jpenalta/fragolinos-medidorCO2/imaxes/alumnos_montando.jpg

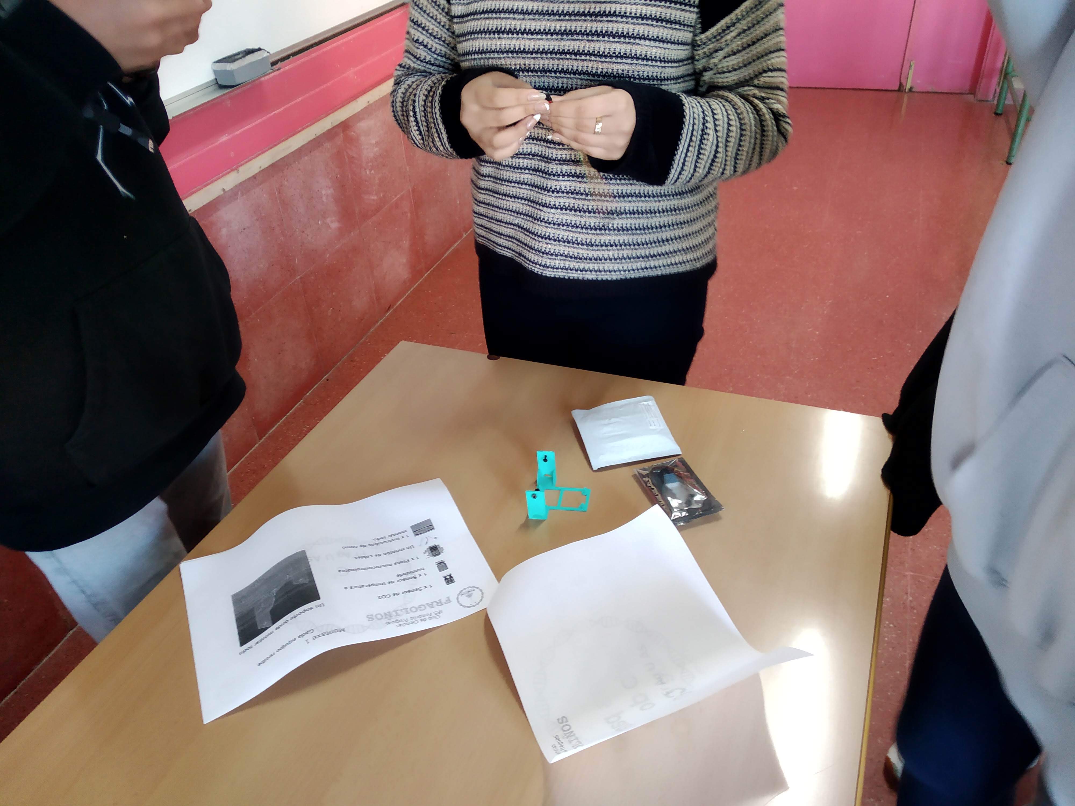
imaxes/alumnos_montando.jpg
