jpenalta/fragolinos-medidorCO2/imaxes/preparados_para_a_aula_2.jpg

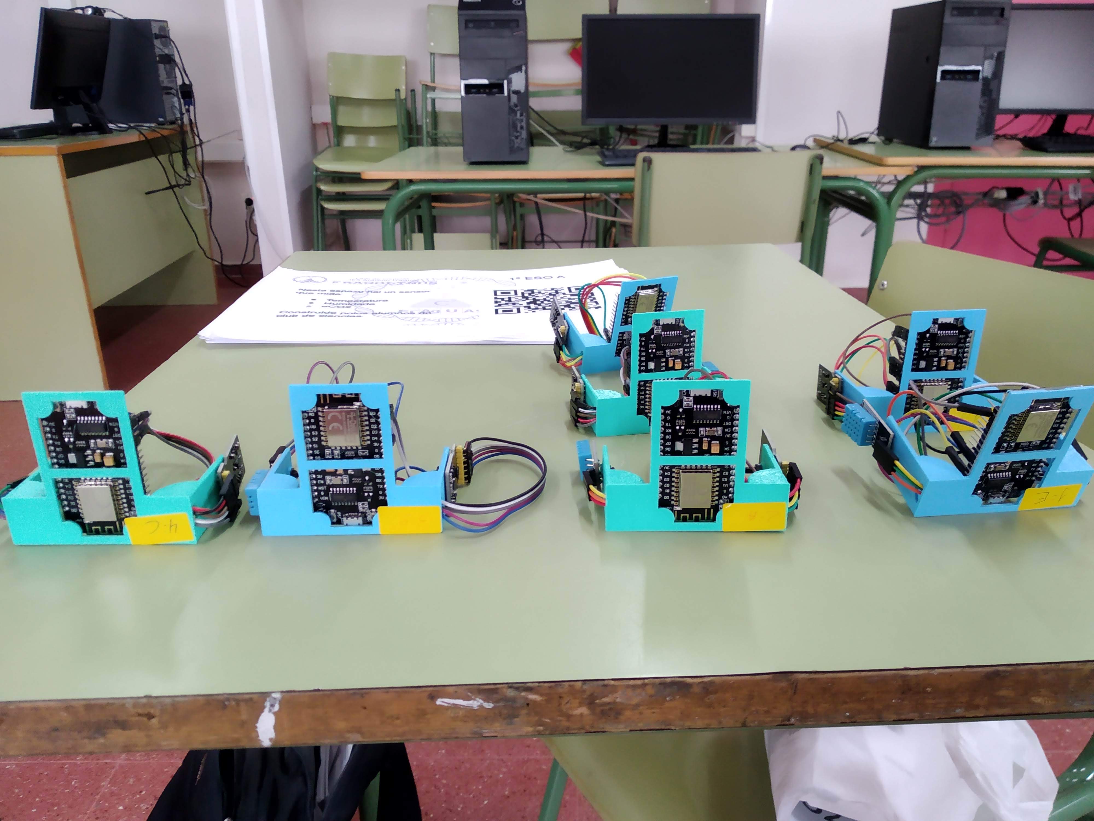
imaxes/preparados_para_a_aula_2.jpg
