jpenalta/fragolinos-medidorCO2/imaxes/soportes_1.jpg

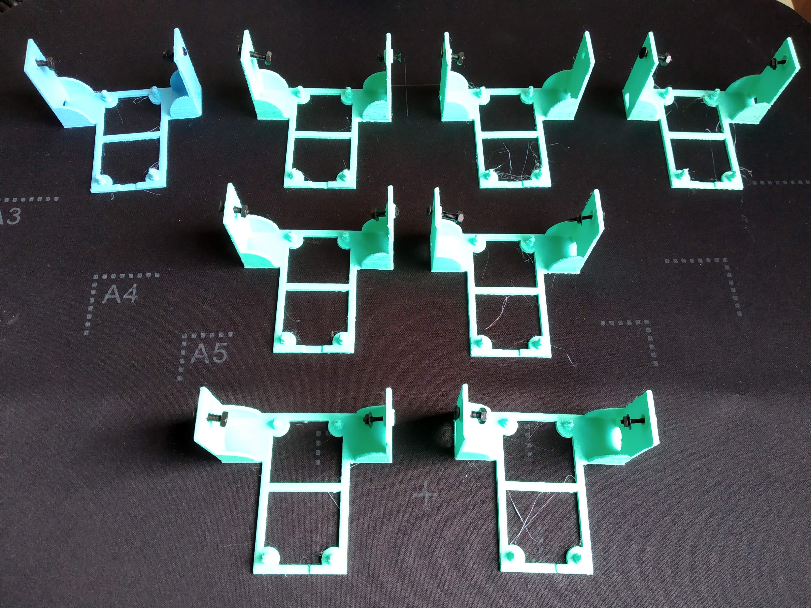
imaxes/soportes_1.jpg
