jpenalta/fragolinos-medidorCO2/imaxes/soportes_2.jpg

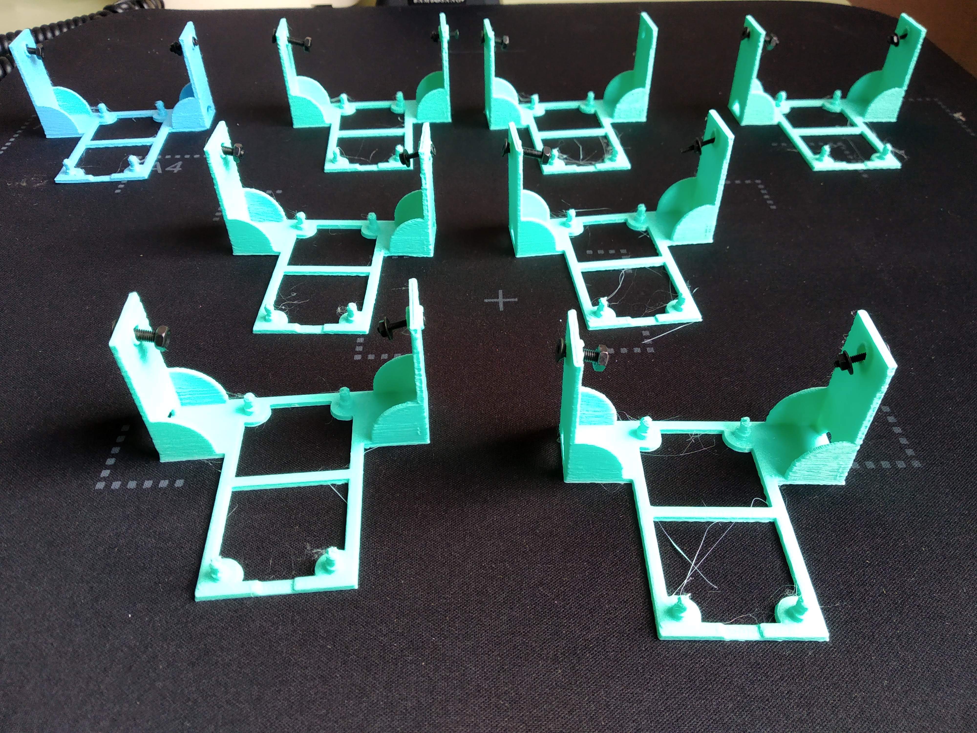
imaxes/soportes_2.jpg
