jpenalta/fragolinos-medidorCO2/src/secrets.h

#define DELAY 29500

#define SECRET_SSID "SSIS DA WIFI"                                // Cambiar polo SSID da wifi
#define SECRET_PASS "CONTRASINAL DA WIFI"                          // Cambiar pola contrasinal da wifi
#define DHTTYPE DHT11
#define DHT_PIN 14  //

#define SECRET_CH_ID 1269673                              // Cambiar polo código do canal
#define SECRET_WRITE_APIKEY "THINGSPEAK_ESCRITURA"               // Cambiar pola chave de escritura
#define SECRET_READ_APIKEY "THINGSPEAK_LECTURA"                 // Cambiar pola chave de lectura
